zimirken/SodiumBulb/20231206_125015.jpg

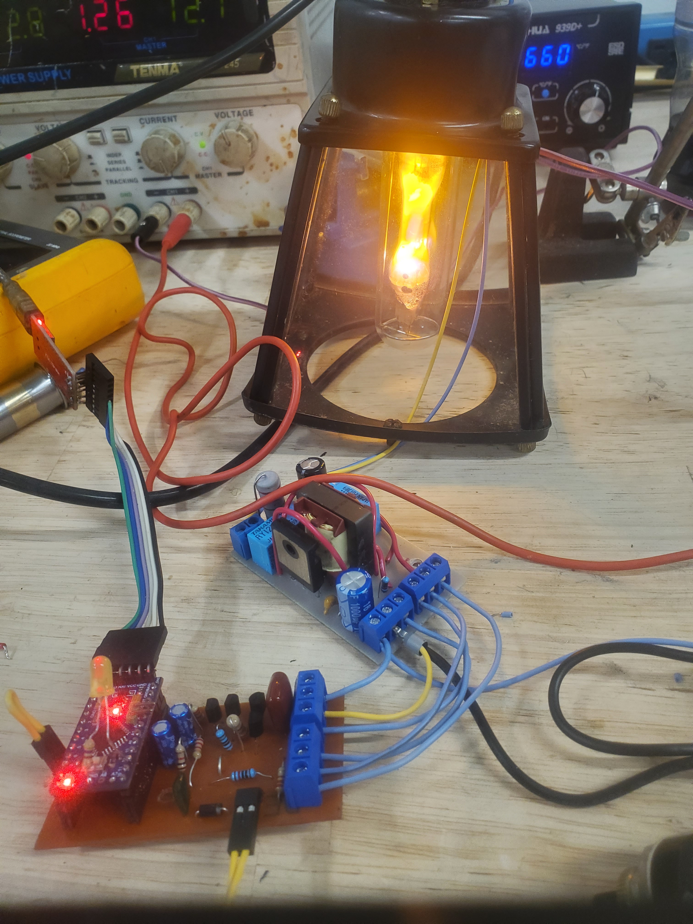
20231206_125015.jpg
