zimirken/SodiumBulb/IMG_0917.jpg

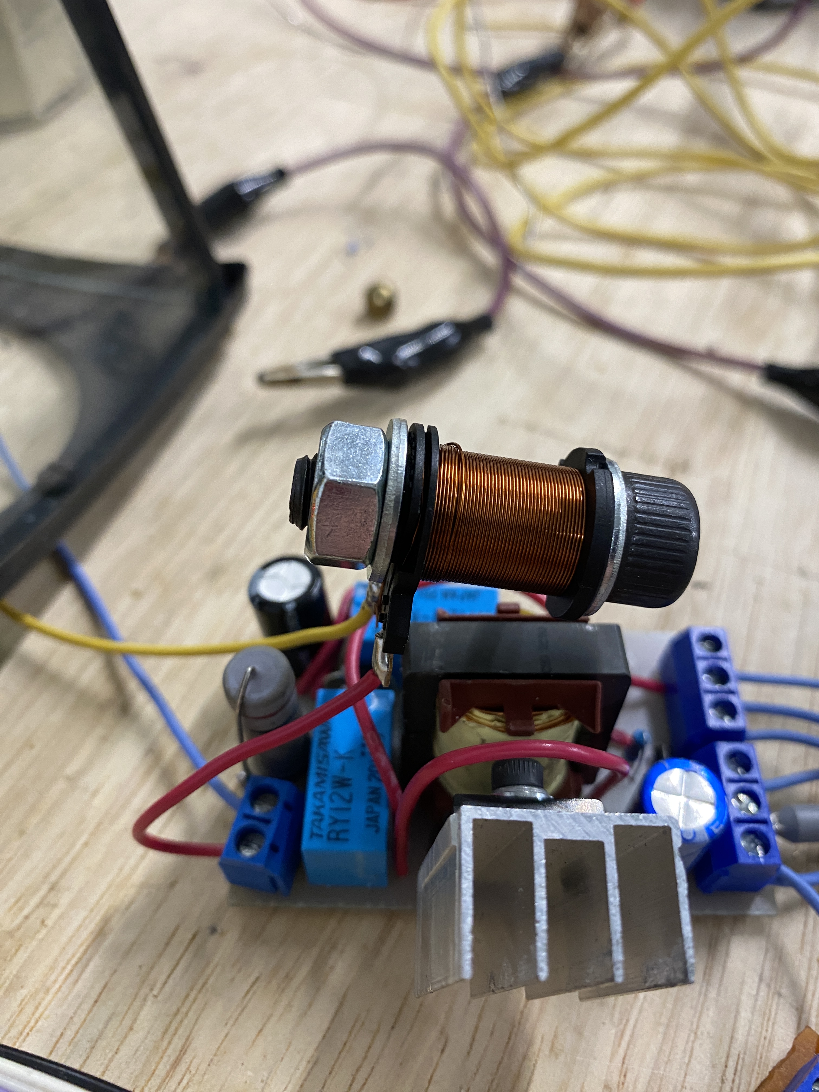
IMG_0917.jpg
