zimirken/SodiumBulb/IMG_0918.jpg

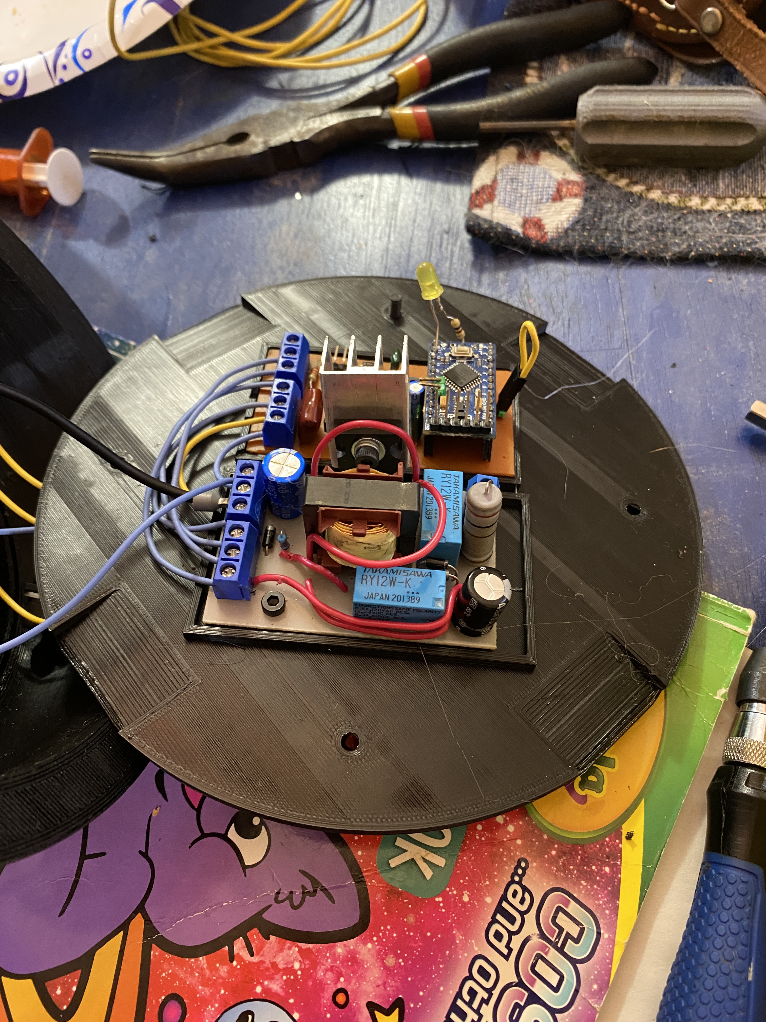
IMG_0918.jpg
