zimirken/SodiumBulb/IMG_0921.jpg

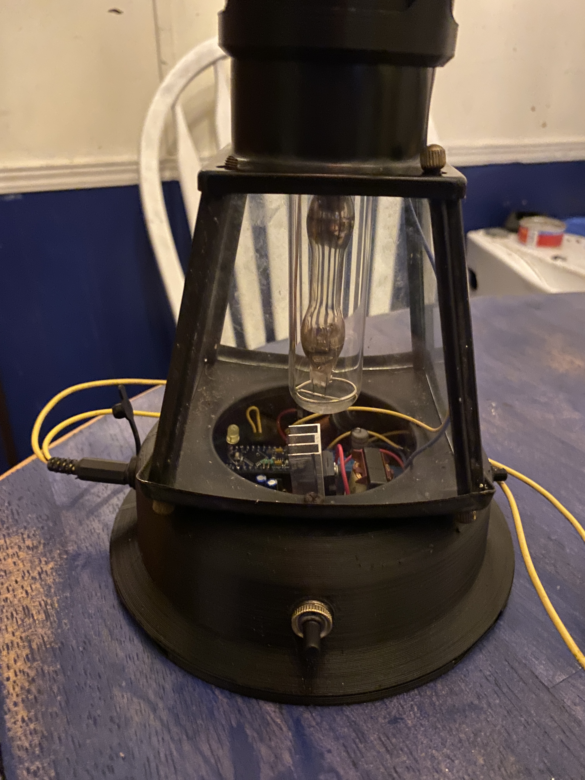
IMG_0921.jpg
